george-p-johnson/gpj-cisco-gsxfy27-networkpuzzle/reference/active-gameplay.png

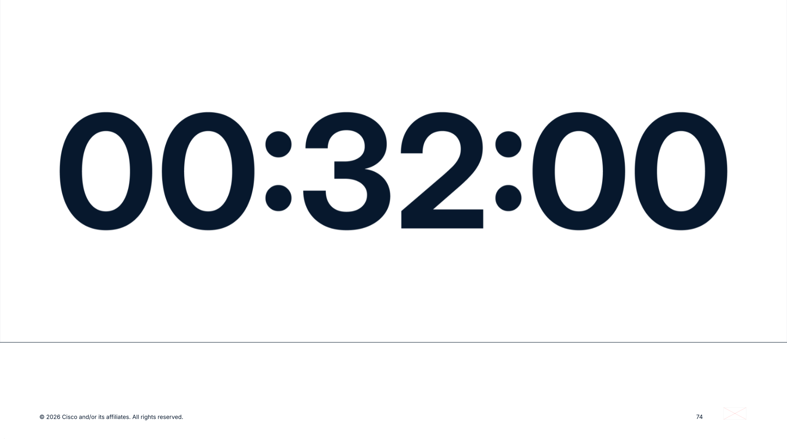
reference/active-gameplay.png
