george-p-johnson/gpj-cisco-gsxfy27-networkpuzzle/reference/Answers_Station3.png

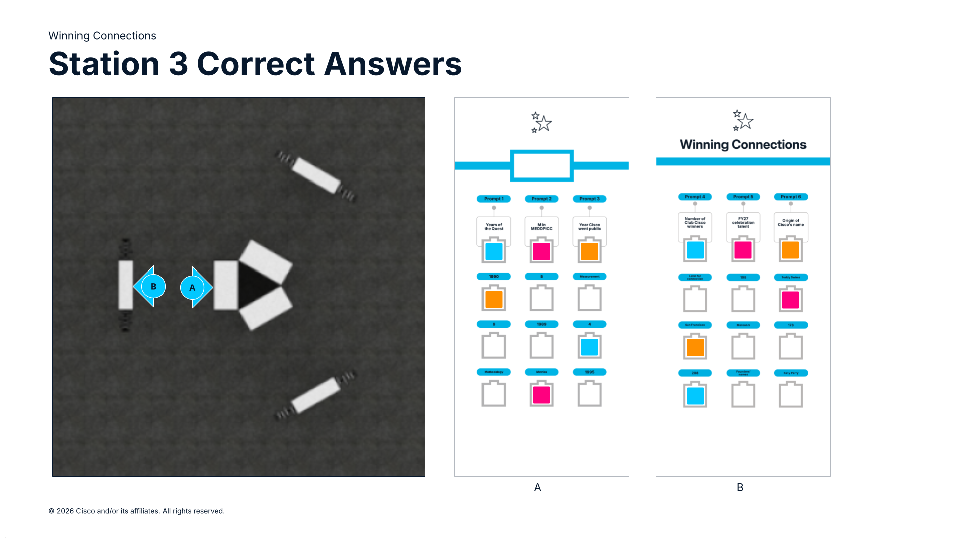
reference/Answers_Station3.png
