george-p-johnson/gpj-cisco-gsxfy27-networkpuzzle/reference/countdown.png

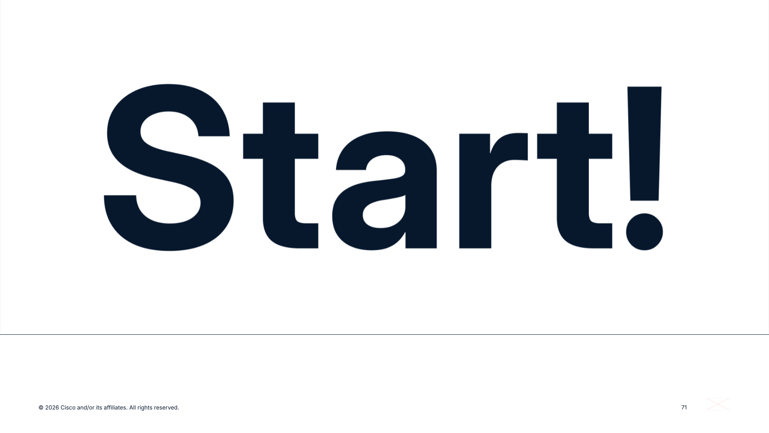
reference/countdown.png
