george-p-johnson/gpj-cisco-gsxfy27-networkpuzzle/reference/results.png

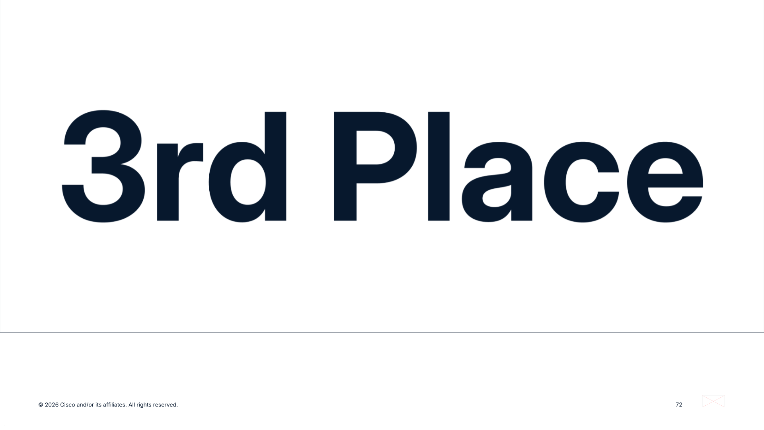
reference/results.png
